NEOgHacking/DMXion_4Port_Node/Firmware/esp-at-5.0.0.0/docs/_static/about-esp-at-solution.png

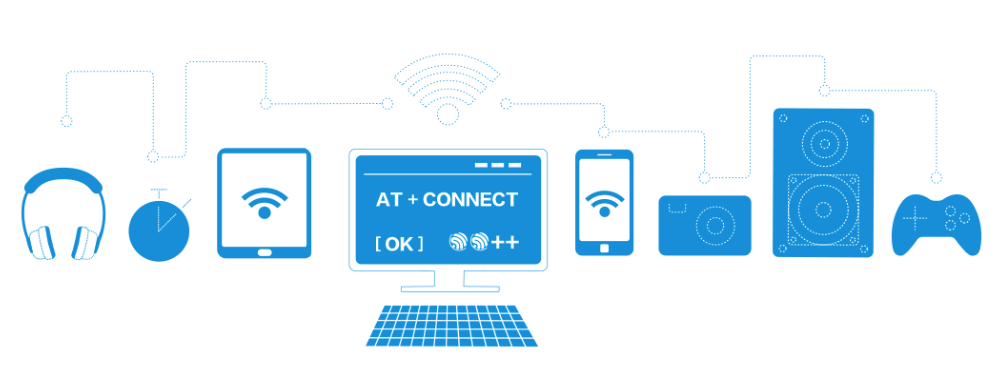
Firmware/esp-at-5.0.0.0/docs/_static/about-esp-at-solution.png
