NEOgHacking/DMXion_4Port_Node/Firmware/esp-at-5.0.0.0/docs/_static/at-sub-release-apply.png

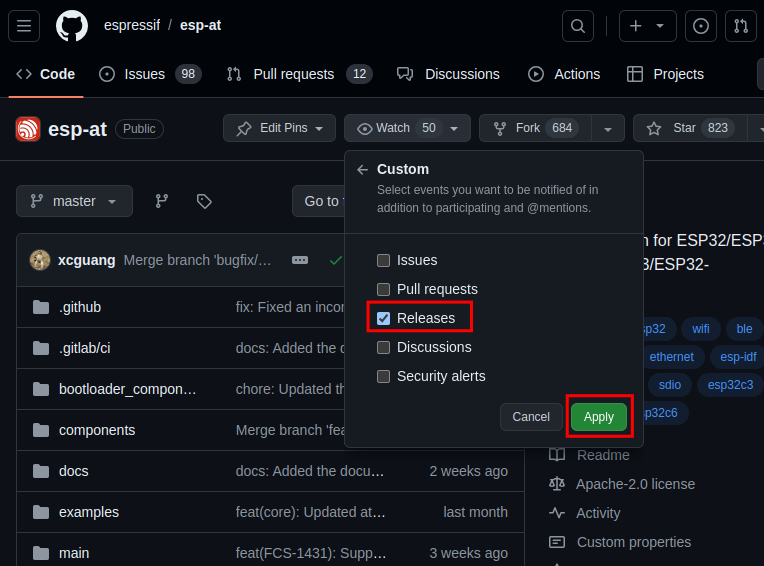
Firmware/esp-at-5.0.0.0/docs/_static/at-sub-release-apply.png
