NEOgHacking/DMXion_4Port_Node/Firmware/esp-at-5.0.0.0/docs/_static/at_command_examples/esp-power-consumption-hardware-connection.png

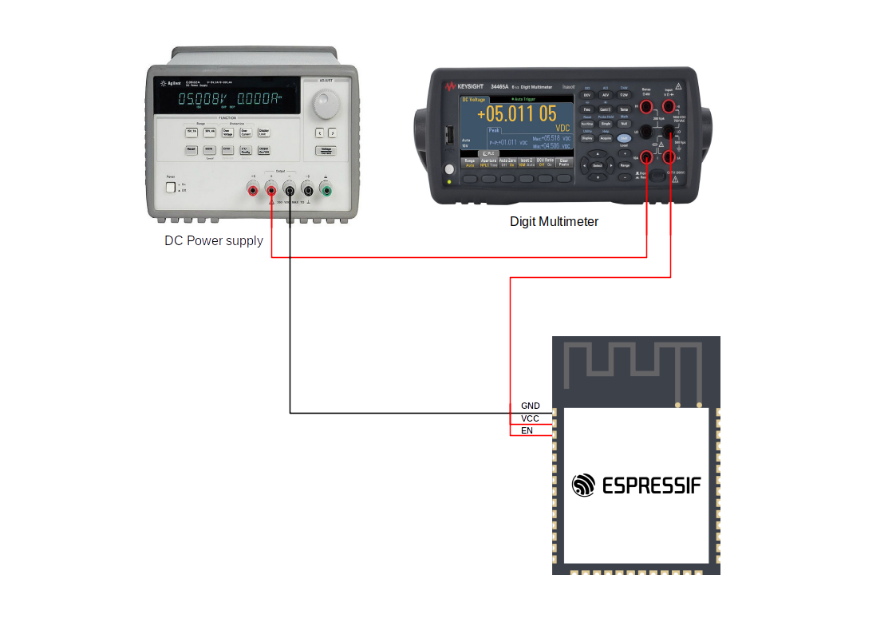
Firmware/esp-at-5.0.0.0/docs/_static/at_command_examples/esp-power-consumption-hardware-connection.png
