NEOgHacking/DMXion_4Port_Node/Firmware/esp-at-5.0.0.0/docs/_static/compile_and_develop/at-py-download.png

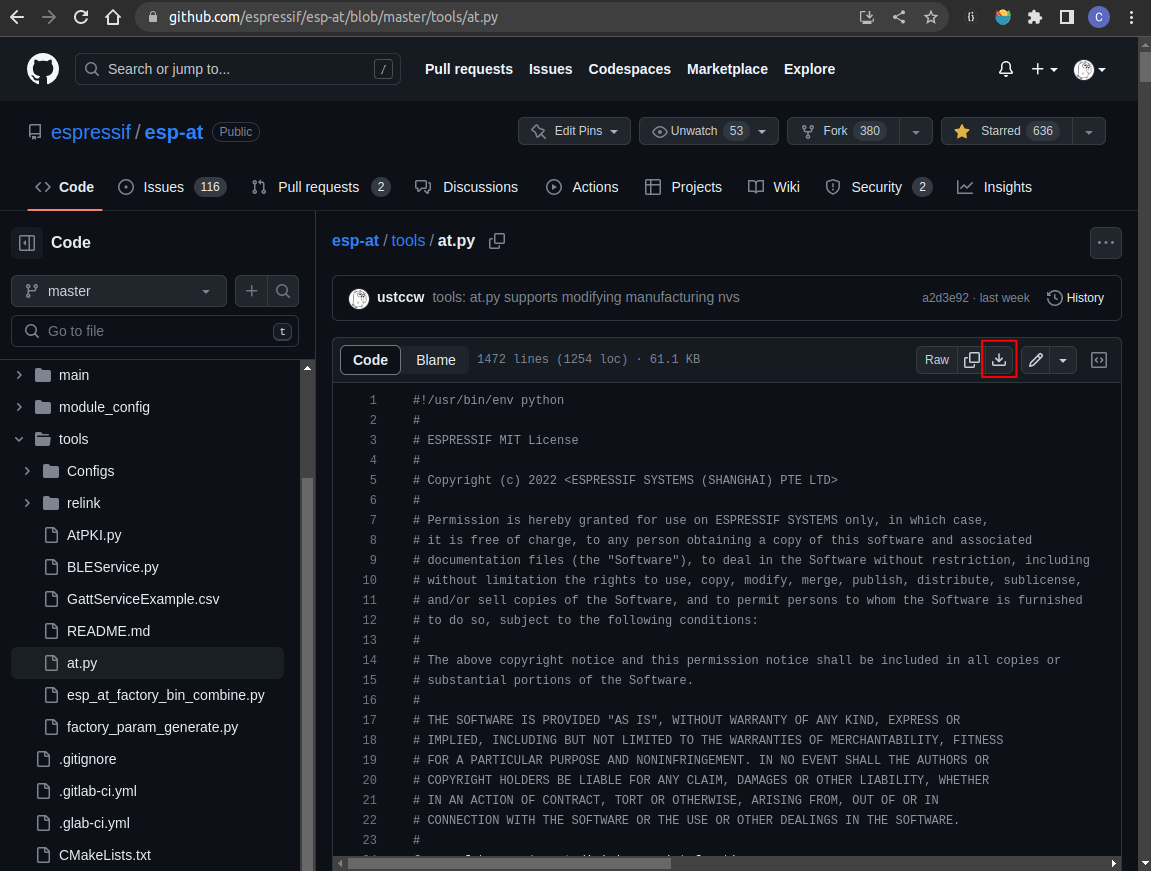
Firmware/esp-at-5.0.0.0/docs/_static/compile_and_develop/at-py-download.png
