NEOgHacking/DMXion_4Port_Node/Firmware/esp-at-5.0.0.0/docs/_static/compile_and_develop/ble_customize_service.png

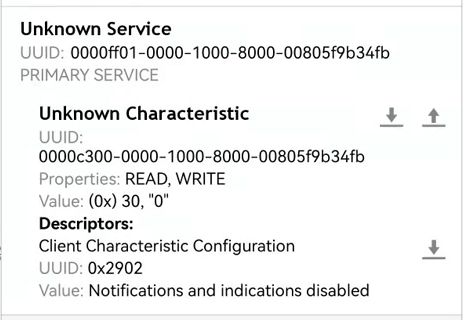
Firmware/esp-at-5.0.0.0/docs/_static/compile_and_develop/ble_customize_service.png
