NEOgHacking/DMXion_4Port_Node/Firmware/esp-at-5.0.0.0/docs/_static/download_temp_version/download-temp-version-github.png

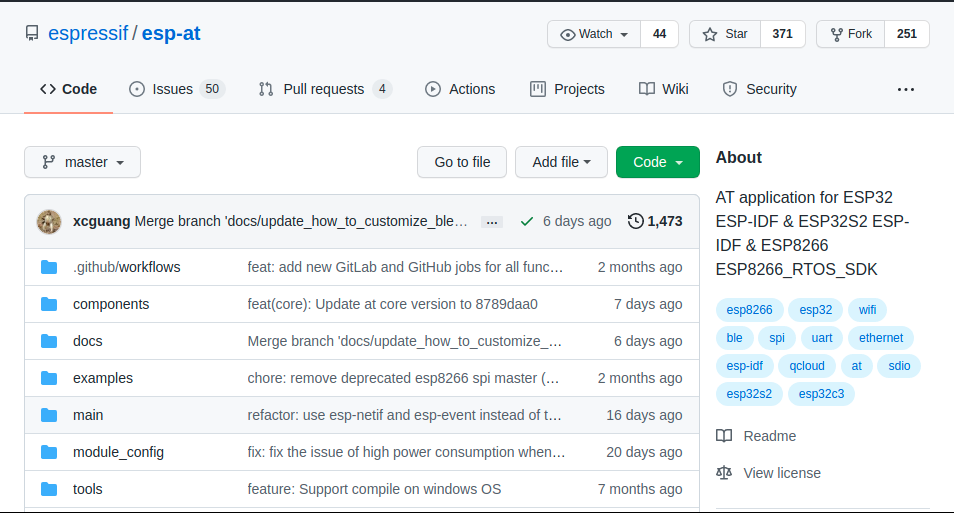
Firmware/esp-at-5.0.0.0/docs/_static/download_temp_version/download-temp-version-github.png
