NEOgHacking/DMXion_4Port_Node/Firmware/esp-at-5.0.0.0/docs/_static/ESP-AT-overview.jpg

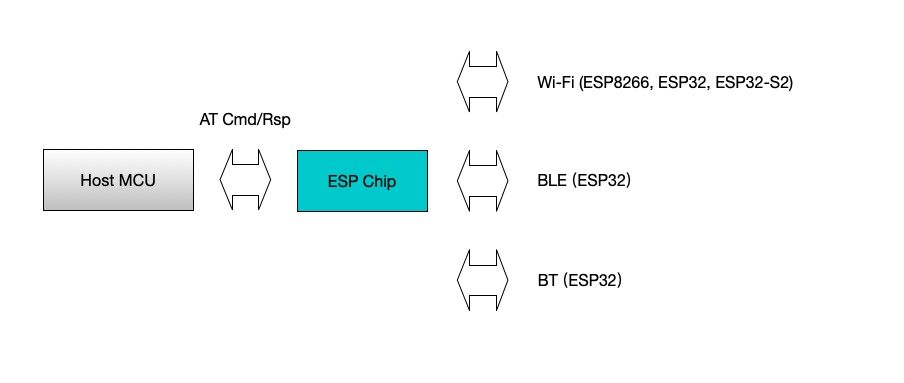
Firmware/esp-at-5.0.0.0/docs/_static/ESP-AT-overview.jpg
