NEOgHacking/DMXion_4Port_Node/Firmware/esp-at-5.0.0.0/docs/_static/get_started/hw_connection/esp32-pico-d4.png

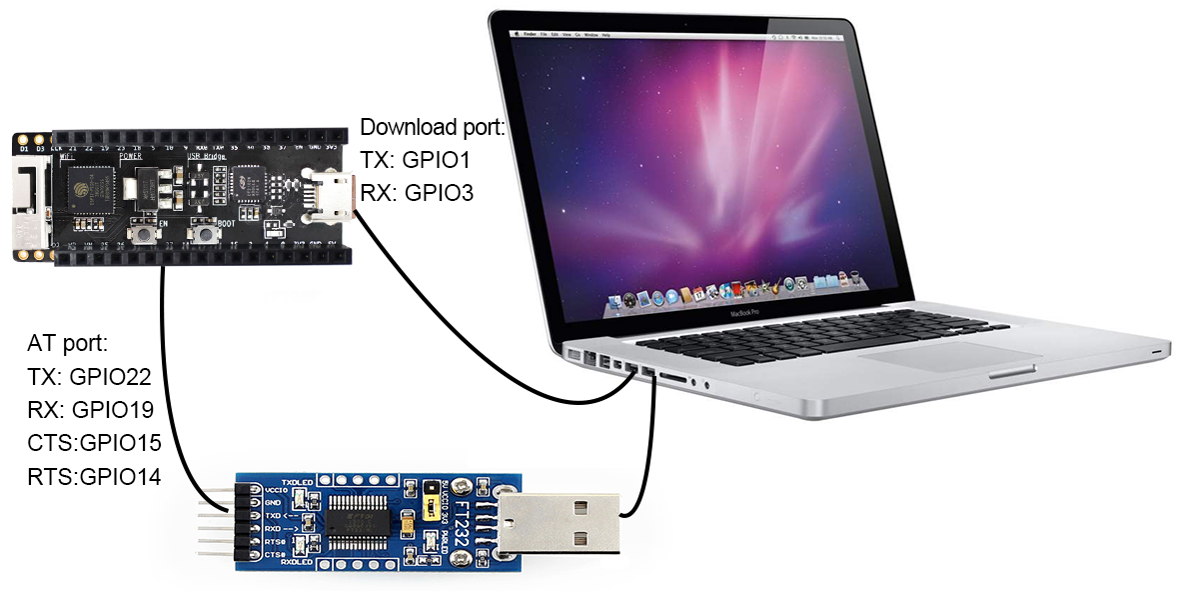
Firmware/esp-at-5.0.0.0/docs/_static/get_started/hw_connection/esp32-pico-d4.png
