NEOgHacking/DMXion_4Port_Node/Firmware/esp-at-5.0.0.0/docs/_static/get_started/hw_connection/hw-connection-what-you-need.png

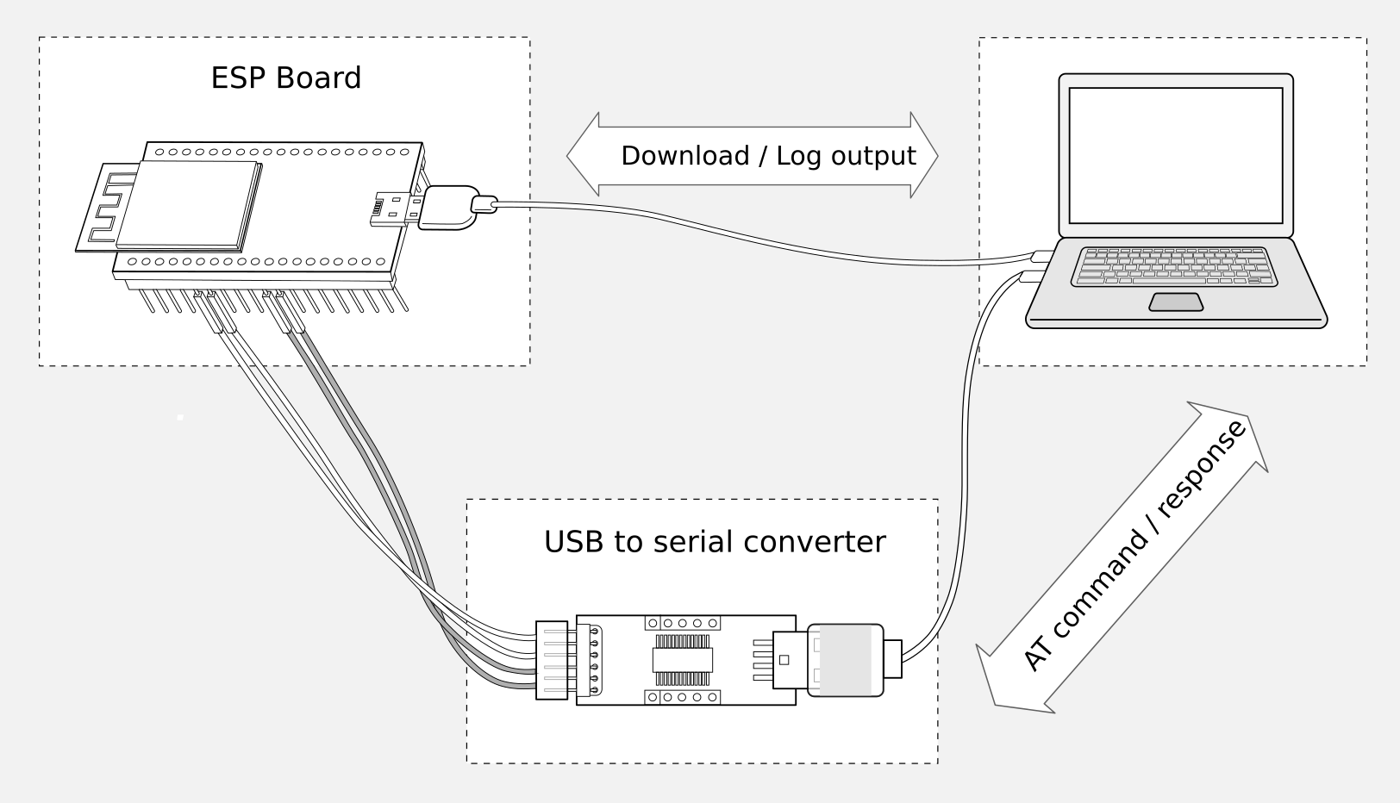
Firmware/esp-at-5.0.0.0/docs/_static/get_started/hw_connection/hw-connection-what-you-need.png
