NEOgHacking/DMXion_4Port_Node/Firmware/esp-at-5.0.0.0/docs/_static/hp-customized-at-commands-and-firmware.png

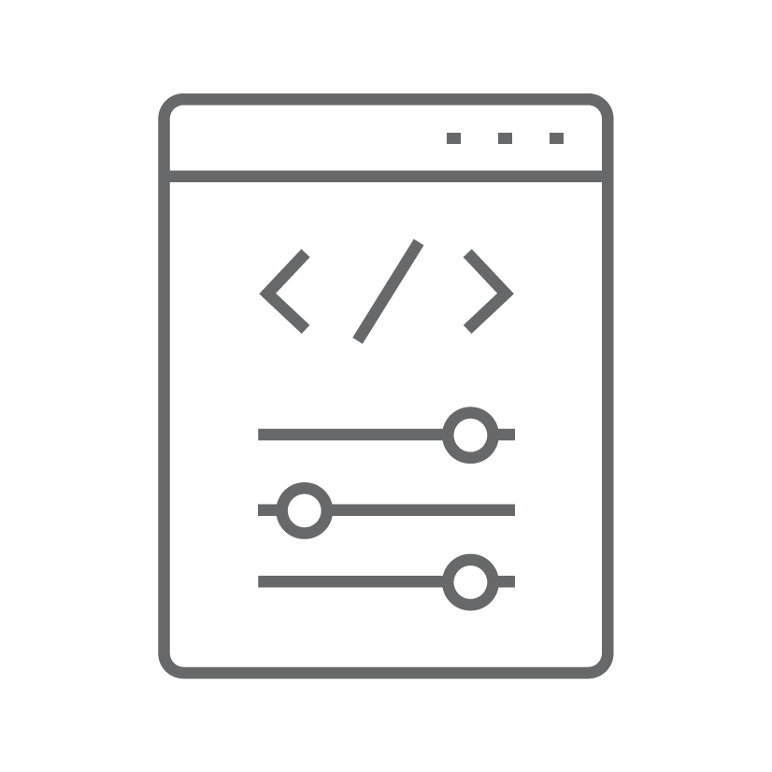
Firmware/esp-at-5.0.0.0/docs/_static/hp-customized-at-commands-and-firmware.png
