NEOgHacking/DMXion_4Port_Node/Firmware/esp-at-5.0.0.0/docs/_static/hp-get-started.png

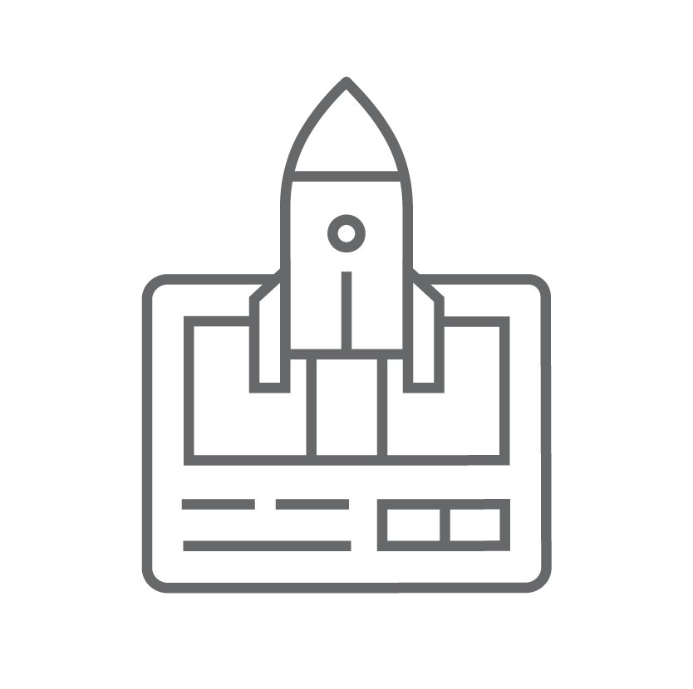
Firmware/esp-at-5.0.0.0/docs/_static/hp-get-started.png
