NEOgHacking/DMXion_4Port_Node/Firmware/esp-at-5.0.0.0/docs/_static/hp-index-of-abbreviations-and-acronyms.png

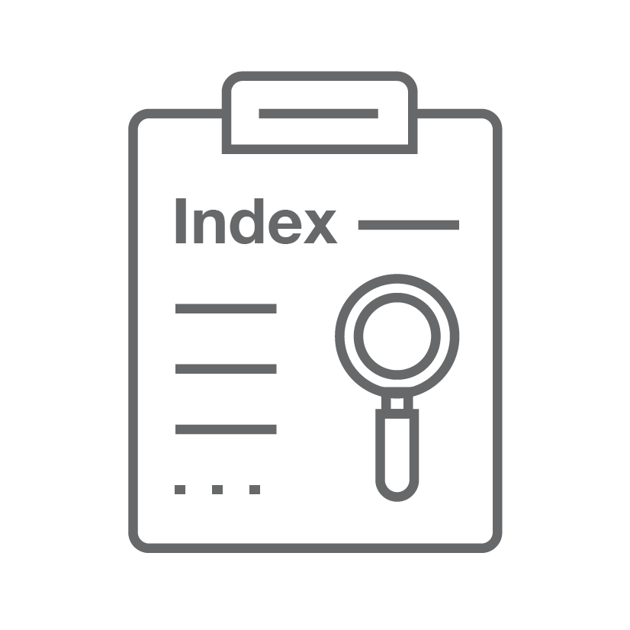
Firmware/esp-at-5.0.0.0/docs/_static/hp-index-of-abbreviations-and-acronyms.png
