NEOgHacking/DMXion_4Port_Node/Firmware/esp-at-5.0.0.0/docs/_static/web_compile/commit-change-s2.png

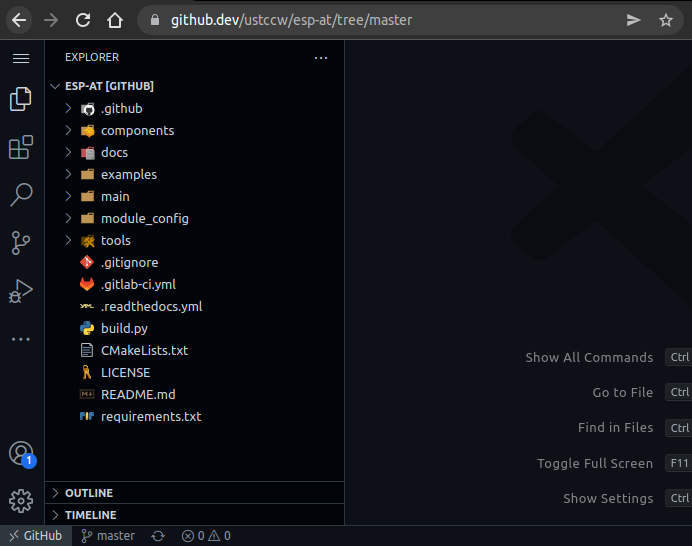
Firmware/esp-at-5.0.0.0/docs/_static/web_compile/commit-change-s2.png
