NEOgHacking/DMXion_4Port_Node/Firmware/esp-at-5.0.0.0/docs/_static/Web_server/captive_portal_auth_pages.png

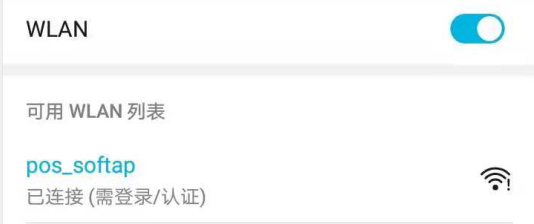
Firmware/esp-at-5.0.0.0/docs/_static/Web_server/captive_portal_auth_pages.png
