NEOgHacking/DMXion_4Port_Node/Firmware/esp-at-5.0.0.0/docs/_static/Web_server/web_brower_get_ap_record_en.png

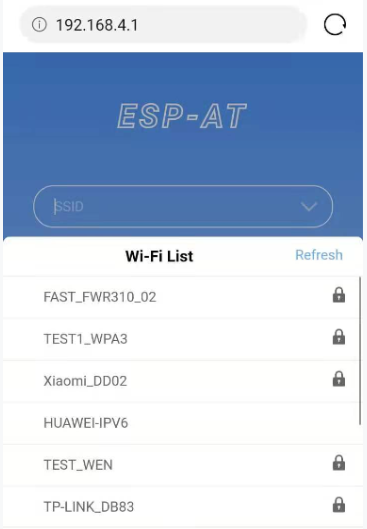
Firmware/esp-at-5.0.0.0/docs/_static/Web_server/web_brower_get_ap_record_en.png
