NEOgHacking/DMXion_4Port_Node/Firmware/esp-at-5.0.0.0/docs/_static/Web_server/web_brower_ota_chose_firmware.png

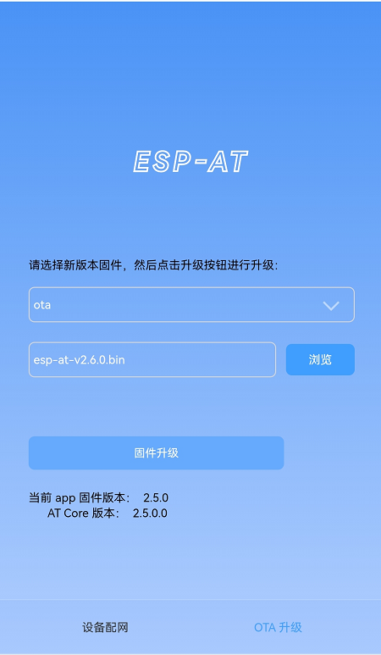
Firmware/esp-at-5.0.0.0/docs/_static/Web_server/web_brower_ota_chose_firmware.png
