NEOgHacking/DMXion_4Port_Node/Firmware/esp-at-5.0.0.0/docs/_static/Web_server/web_brower_wifi_ap_en.png

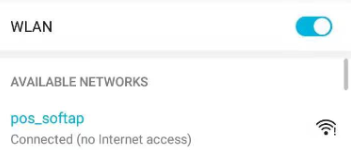
Firmware/esp-at-5.0.0.0/docs/_static/Web_server/web_brower_wifi_ap_en.png
