NEOgHacking/DMXion_4Port_Node/Firmware/esp-at-5.0.0.0/docs/_static/Web_server/web_wechat_connect_router.png

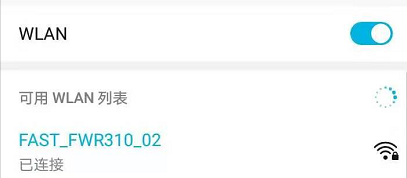
Firmware/esp-at-5.0.0.0/docs/_static/Web_server/web_wechat_connect_router.png
