NEOgHacking/DMXion_4Port_Node/Firmware/esp-at-5.0.0.0/docs/_static/Web_server/web_wechat_enter_local_password.png

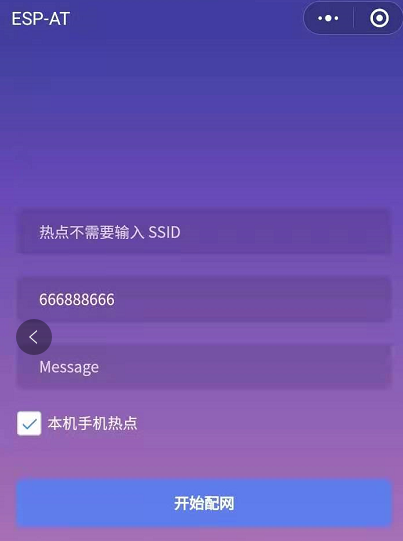
Firmware/esp-at-5.0.0.0/docs/_static/Web_server/web_wechat_enter_local_password.png
