NEOgHacking/DMXion_4Port_Node/Firmware/esp-at-5.0.0.0/docs/_static/Web_server/web_wechat_update_router_info.png

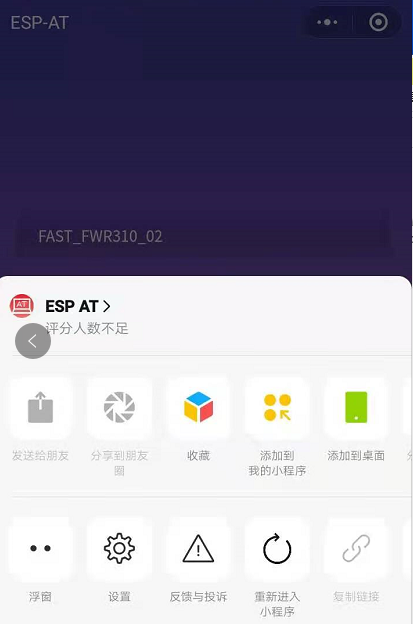
Firmware/esp-at-5.0.0.0/docs/_static/Web_server/web_wechat_update_router_info.png
