NEOgHacking/DMXion_4Port_Node/Firmware/esp-at-5.0.0.0/docs/img/esp32at-log.png

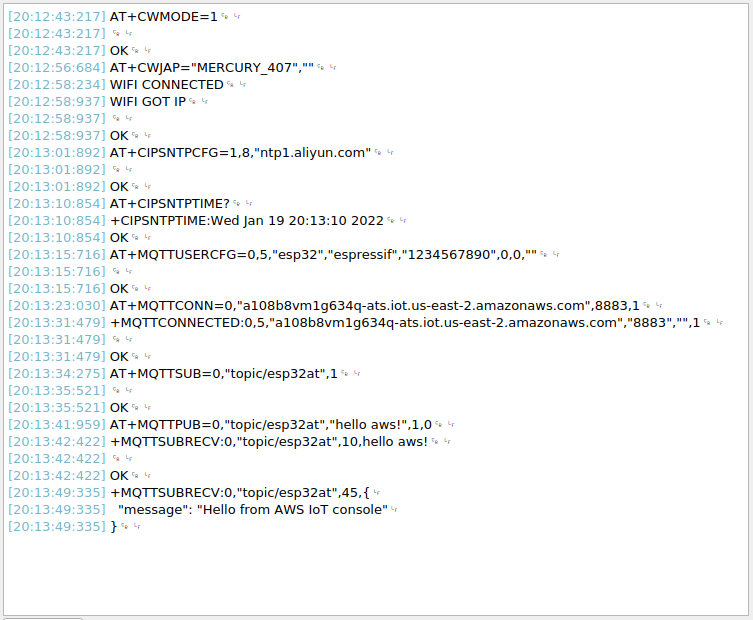
Firmware/esp-at-5.0.0.0/docs/img/esp32at-log.png
