NEOgHacking/DMXion_4Port_Node/Firmware/esp-at-5.0.0.0/examples/at_sdio_host/res/sdio_dataflow.jpg

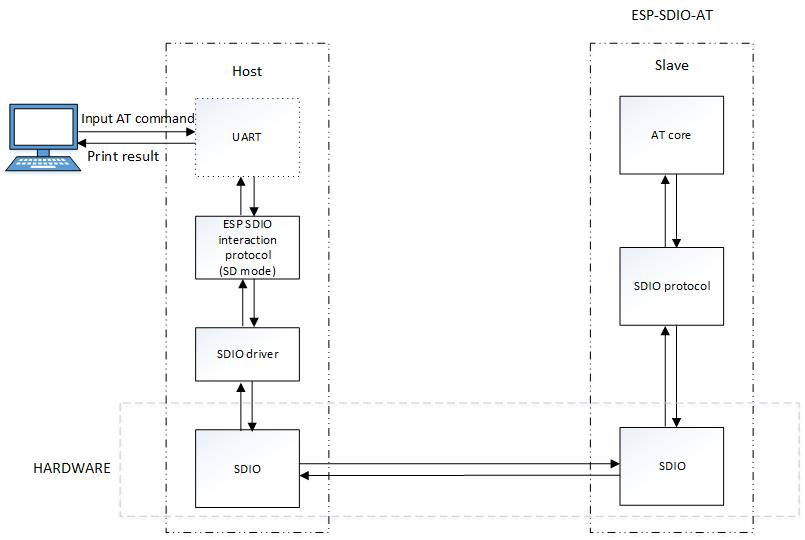
Firmware/esp-at-5.0.0.0/examples/at_sdio_host/res/sdio_dataflow.jpg
