NEOgHacking/DMXion_4Port_Node/Firmware/esp-at-5.0.0.0/examples/at_spi_master/sdspi/res/data_flow.png

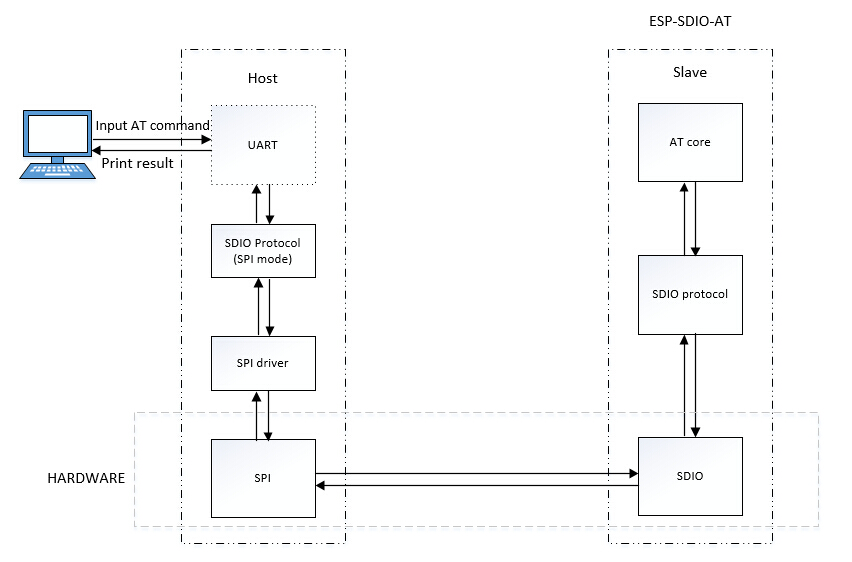
Firmware/esp-at-5.0.0.0/examples/at_spi_master/sdspi/res/data_flow.png
