NEOgHacking/DMXion_4Port_Node/Firmware/esp-at-5.0.0.0/examples/at_spi_master/spi/esp32_c_series/res/mcu_read_data.png

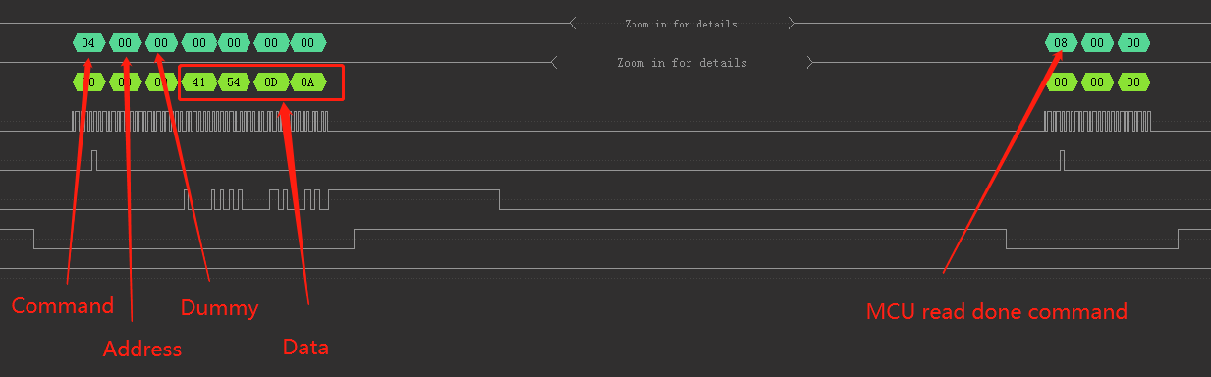
Firmware/esp-at-5.0.0.0/examples/at_spi_master/spi/esp32_c_series/res/mcu_read_data.png
