NEOgHacking/DMXion_4Port_Node/Firmware/esp-at-5.0.0.0/docs/zh_CN/Get_Started/Downloading_guide.rst

下载指导
==========

{IDF_TARGET_MODULE_NAME: default="undefined", esp32="ESP32-WROOM-32", esp32c2="ESP8684-MINI-1", esp32c3="ESP32-C3-MINI-1", esp32c5="ESP32-C5-WROOM-1", esp32c6="ESP32-C6-MINI-1", esp32c61="ESP32-C61-WROOM-1", esp32s2="ESP32-S2-MINI"}
{IDF_TARGET_FACTORY_BIN: default="undefined", esp32="ESP32-WROOM-32-AT-V3.2.0.0", esp32c2="ESP32C2-4MB-AT-V3.3.0.0", esp32c3="ESP32-C3-MINI-1-AT-V3.3.0.0", esp32c5="ESP32C5-4MB-AT-V5.0.0.0", esp32c6="ESP32C6-4MB-AT-V4.0.0.0", esp32c61="ESP32C61-4MB-AT-V5.0.0.0", esp32s2="ESP32-S2-MINI-AT-V3.4.0.0"}

:link_to_translation:`en:[English]`

本文档以 {IDF_TARGET_MODULE_NAME} 模组为例，介绍如何下载 {IDF_TARGET_MODULE_NAME} 模组对应的 AT 固件，以及如何将固件烧录到模组上，其它 {IDF_TARGET_NAME} 系列模组也可参考本文档。

下载和烧录 AT 固件之前，请确保您已正确连接所需硬件，具体可参考 :doc:`Hardware_connection`。

对于不同系列的模组，AT 默认固件所支持的命令会有所差异。具体可参考 :doc:`/Compile_and_Develop/esp-at_firmware_differences`。

.. _download-at-firmware:

下载 AT 固件
-------------

请按照以下步骤将 AT 固件下载至 PC：

- 前往 :doc:`../AT_Binary_Lists/index`
- 找到您的模组所对应的 AT 固件
- 点击相应链接进行下载

此处，我们下载了 {IDF_TARGET_MODULE_NAME} 对应的 ``{IDF_TARGET_FACTORY_BIN}`` 固件，该固件的目录结构及其中各个 bin 文件介绍如下，其它 {IDF_TARGET_NAME} 系列模组固件的目录结构及 bin 文件也可参考如下介绍：

.. code-block:: none

   .
   ├── at_customize.bin                 // 二级分区表
   ├── bootloader                       // bootloader
   │   └── bootloader.bin
   ├── customized_partitions            // AT 自定义 bin 文件
         ├── mfg_nvs.csv                  // 量产 NVS 分区的原始数据
   │   └── mfg_nvs.bin                  // 量产 NVS 分区 bin 文件
   ├── download.config                  // 烧录固件的参数
   ├── esp-at.bin                       // AT 应用固件
   ├── esp-at.elf
   ├── esp-at.map
   ├── factory                          // 量产所需打包好的 bin 文件
   │   └── factory_XXX.bin
   ├── flasher_args.json                // 下载参数信息新的格式
   ├── ota_data_initial.bin             // ota data 区初始值
   ├── partition_table                  // 一级分区列表
   │   └── partition-table.bin
   └── sdkconfig                        // AT 固件对应的编译配置

其中，``download.config`` 文件包含烧录固件的参数：

.. only:: esp32

   .. code-block:: none

      --flash_mode dio --flash_freq 40m --flash_size 4MB
      0x1000 bootloader/bootloader.bin
      0x8000 partition_table/partition-table.bin
      0x10000 ota_data_initial.bin
      0x20000 at_customize.bin
      0x21000 customized_partitions/mfg_nvs.bin
      0x100000 esp-at.bin

.. only:: esp32c2

   .. code-block:: none

      --flash_mode dio --flash_freq 60m --flash_size 4MB
      0x0 bootloader/bootloader.bin
      0x8000 partition_table/partition-table.bin
      0xd000 ota_data_initial.bin
      0x1e000 at_customize.bin
      0x1f000 customized_partitions/mfg_nvs.bin
      0x60000 esp-at.bin

.. only:: esp32c3

   .. code-block:: none

      --flash_mode dio --flash_freq 40m --flash_size 4MB
      0x0 bootloader/bootloader.bin
      0x8000 partition_table/partition-table.bin
      0xd000 ota_data_initial.bin
      0x1e000 at_customize.bin
      0x1f000 customized_partitions/mfg_nvs.bin
      0x60000 esp-at.bin

.. only:: esp32c5

   .. code-block:: none

      --flash_mode dio --flash_freq 80m --flash_size 4MB
      0x2000 bootloader/bootloader.bin
      0xc000 partition_table/partition-table.bin
      0xd000 ota_data_initial.bin
      0x30000 at_customize.bin
      0x31000 customized_partitions/mfg_nvs.bin
      0xa0000 esp-at.bin

.. only:: esp32c6

   .. code-block:: none

      --flash_mode dio --flash_freq 80m --flash_size 4MB
      0x0 bootloader/bootloader.bin
      0x8000 partition_table/partition-table.bin
      0xd000 ota_data_initial.bin
      0x1e000 at_customize.bin
      0x1f000 customized_partitions/mfg_nvs.bin
      0x60000 esp-at.bin

.. only:: esp32c61

   .. code-block:: none

      --flash_mode dio --flash_freq 80m --flash_size 4MB
      0x0 bootloader/bootloader.bin
      0xc000 partition_table/partition-table.bin
      0xd000 ota_data_initial.bin
      0x30000 at_customize.bin
      0x31000 customized_partitions/mfg_nvs.bin
      0xa0000 esp-at.bin

.. only:: esp32s2

   .. code-block:: none

      --flash_mode dio --flash_freq 80m --flash_size 4MB
      0x1000 bootloader/bootloader.bin
      0x8000 partition_table/partition-table.bin
      0x10000 ota_data_initial.bin
      0x20000 at_customize.bin
      0x21000 customized_partitions/mfg_nvs.bin
      0x100000 esp-at.bin

.. list::

   - ``--flash_mode dio`` 代表此固件采用的 flash dio 模式进行编译；
   :esp32 or esp32c3: - ``--flash_freq 40m`` 代表此固件采用的 flash 通讯频率为 40 MHz；
   :esp32c2: - ``--flash_freq 60m`` 代表此固件采用的 flash 通讯频率为 60 MHz；
   :esp32c5 or esp32c6 or esp32c61 or esp32s2: - ``--flash_freq 80m`` 代表此固件采用的 flash 通讯频率为 80 MHz；
   - ``--flash_size 4MB`` 代表此固件适用的 flash 最小为 4 MB；
   :esp32 or esp32s2: - ``0x10000 ota_data_initial.bin`` 代表在 ``0x10000`` 地址烧录 ``ota_data_initial.bin`` 文件。
   :esp32c2 or esp32c3 or esp32c5 or esp32c6 or esp32c61: - ``0xd000 ota_data_initial.bin`` 代表在 ``0xd000`` 地址烧录 ``ota_data_initial.bin`` 文件。

.. _flash-at-firmware-into-your-device:

烧录 AT 固件至设备
-------------------

请根据您的操作系统选择对应的烧录方法。

Windows
^^^^^^^^

开始烧录之前，请下载 Windows `Flash 下载工具 <https://dl.espressif.com/public/flash_download_tool.zip>`_，详细指导可参阅 `Flash 下载工具用户指南 <https://docs.espressif.com/projects/esp-test-tools/zh_CN/latest/{IDF_TARGET_PATH_NAME}/production_stage/tools/flash_download_tool.html>`_。

- 打开 Flash 下载工具；
- 选择芯片类型；（此处，我们选择 ``{IDF_TARGET_NAME}``。）
- 根据您的需求选择一种工作模式；（此处，我们选择 ``develop``。)
- 根据您的需求选择一种下载接口；（此处，我们选择 ``uart``。)

固件下载配置选择

   固件下载配置选择

- 将 AT 固件烧录至设备，以下两种方式任选其一：

   - 直接下载打包好的量产固件（即 ``build/factory`` 目录下的 ``factory_XXX.bin``）至 ``0x0`` 地址：勾选 "DoNotChgBin"，使用量产固件的默认配置；

     下载至单个地址界面图

        下载至单个地址界面图（点击放大）

   - 分开下载多个 bin 文件至不同的地址：根据 ``download.config`` 文件进行配置，请勿勾选 "DoNotChgBin"；

     下载至多个地址界面图

        下载至多个地址界面图（点击放大）

为了避免烧录出现问题，请查看开发板的下载接口的 COM 端口号，并从 "COM:" 下拉列表中选择该端口号。有关如何查看端口号的详细介绍请参考 `在 Windows 上查看端口 <https://docs.espressif.com/projects/esp-idf/zh_CN/latest/{IDF_TARGET_PATH_NAME}/get-started/establish-serial-connection.html#windows>`_。 

烧录完成后, 请 `检查 AT 固件是否烧录成功`_。

Linux 或 macOS
^^^^^^^^^^^^^^^

开始烧录之前，请安装 `esptool.py <https://github.com/espressif/esptool>`_。

以下两种方式任选其一，将 AT 固件烧录至设备：

- 分开下载多个 bin 文件至不同的地址：输入以下命令，替换 ``PORTNAME`` 和 ``download.config`` 参数；

  .. code-block:: none

      esptool.py --chip auto --port PORTNAME --baud 115200 --before default_reset --after hard_reset write_flash -z download.config

  将 ``PORTNAME`` 替换成开发板的下载接口名称，若您无法确定该接口名称，请参考 `在 Linux 和 macOS 上查看端口 <https://docs.espressif.com/projects/esp-idf/zh_CN/latest/{IDF_TARGET_PATH_NAME}/get-started/establish-serial-connection.html#linux-macos>`_。

  将 ``download.config`` 替换成该文件里的参数列表。

  以下是将固件烧录至 {IDF_TARGET_MODULE_NAME} 模组输入的命令：

   .. only:: esp32

      .. code-block:: none

         esptool.py --chip auto --port /dev/tty.usbserial-0001 --baud 115200 --before default_reset --after hard_reset write_flash -z --flash_mode dio --flash_freq 40m --flash_size 4MB 0x8000 partition_table/partition-table.bin 0x10000 ota_data_initial.bin 0x1000 bootloader/bootloader.bin 0x100000 esp-at.bin 0x20000 at_customize.bin 0x21000 customized_partitions/mfg_nvs.bin

   .. only:: esp32c2

      .. code-block:: none

         esptool.py --chip auto --port /dev/tty.usbserial-0001 --baud 115200 --before default_reset --after hard_reset write_flash -z --flash_mode dio --flash_freq 60m --flash_size 4MB 0x0 bootloader/bootloader.bin 0x60000 esp-at.bin 0x8000 partition_table/partition-table.bin 0xd000 ota_data_initial.bin 0x1e000 at_customize.bin 0x1f000 customized_partitions/mfg_nvs.bin

   .. only:: esp32c3

      .. code-block:: none

         esptool.py --chip auto --port /dev/tty.usbserial-0001 --baud 115200 --before default_reset --after hard_reset write_flash -z --flash_mode dio --flash_freq 40m --flash_size 4MB 0x8000 partition_table/partition-table.bin 0xd000 ota_data_initial.bin 0x0 bootloader/bootloader.bin 0x60000 esp-at.bin 0x1e000 at_customize.bin 0x1f000 customized_partitions/mfg_nvs.bin

   .. only:: esp32c5

      .. code-block:: none

         esptool.py --chip auto --port /dev/tty.usbserial-0001 --baud 115200 --before default_reset --after hard_reset write_flash -z --flash_mode dio --flash_freq 80m --flash_size 4MB 0xc000 partition_table/partition-table.bin 0xd000 ota_data_initial.bin 0x2000 bootloader/bootloader.bin 0xa0000 esp-at.bin 0x30000 at_customize.bin 0x31000 customized_partitions/mfg_nvs.bin

   .. only:: esp32c6

      .. code-block:: none

         esptool.py --chip auto --port /dev/tty.usbserial-0001 --baud 115200 --before default_reset --after hard_reset write_flash -z --flash_mode dio --flash_freq 80m --flash_size 4MB 0x8000 partition_table/partition-table.bin 0xd000 ota_data_initial.bin 0x0 bootloader/bootloader.bin 0x60000 esp-at.bin 0x1e000 at_customize.bin 0x1f000 customized_partitions/mfg_nvs.bin

   .. only:: esp32c61

      .. code-block:: none

         esptool.py --chip auto --port /dev/tty.usbserial-0001 --baud 115200 --before default_reset --after hard_reset write_flash -z --flash_mode dio --flash_freq 80m --flash_size 4MB 0xc000 partition_table/partition-table.bin 0xd000 ota_data_initial.bin 0x0 bootloader/bootloader.bin 0xa0000 esp-at.bin 0x30000 at_customize.bin 0x31000 customized_partitions/mfg_nvs.bin

   .. only:: esp32s2

      .. code-block:: none

         esptool.py --chip auto --port /dev/tty.usbserial-0001 --baud 115200 --before default_reset --after hard_reset write_flash -z --flash_mode dio --flash_freq 40m --flash_size 4MB 0x0 bootloader/bootloader.bin 0x60000 esp-at.bin 0x8000 partition_table/partition-table.bin 0xd000 ota_data_initial.bin 0x1e000 at_customize.bin 0x1f000 customized_partitions/mfg_nvs.bin

- 直接下载打包好的量产固件至 ``0x0`` 地址：输入以下命令，替换 ``PORTNAME`` 和 ``FILEDIRECTORY`` 参数；

  .. code-block:: none

     esptool.py --chip auto --port PORTNAME --baud 115200 --before default_reset --after hard_reset write_flash -z --flash_mode dio --flash_freq 40m --flash_size 4MB 0x0 FILEDIRECTORY

  将 ``PORTNAME`` 替换成开发板的下载接口名称，若您无法确定该接口名称，请参考 `在 Linux 和 macOS 上查看端口 <https://docs.espressif.com/projects/esp-idf/zh_CN/latest/{IDF_TARGET_PATH_NAME}/get-started/establish-serial-connection.html#linux-macos>`_。

  将 ``FILEDIRECTORY`` 替换成打包好的量产固件的文件路径，通常情况下，文件路径是 ``factory/XXX.bin``。

  以下是将固件烧录至 {IDF_TARGET_MODULE_NAME} 模组输入的命令：

   .. only:: esp32

      .. code-block:: none

         esptool.py --chip auto --port /dev/tty.usbserial-0001 --baud 115200 --before default_reset --after hard_reset write_flash -z --flash_mode dio --flash_freq 40m --flash_size 4MB 0x0 factory/factory_WROOM-32.bin

   .. only:: esp32c2

      .. code-block:: none

         esptool.py --chip auto --port /dev/tty.usbserial-0001 --baud 115200 --before default_reset --after hard_reset write_flash -z --flash_mode dio --flash_freq 60m --flash_size 4MB 0x0 factory/factory_ESP32C2-4MB.bin

   .. only:: esp32c3

      .. code-block:: none

         esptool.py --chip auto --port /dev/tty.usbserial-0001 --baud 115200 --before default_reset --after hard_reset write_flash -z --flash_mode dio --flash_freq 40m --flash_size 4MB 0x0 factory/factory_MINI-1.bin

   .. only:: esp32c5

      .. code-block:: none

         esptool.py --chip auto --port /dev/tty.usbserial-0001 --baud 115200 --before default_reset --after hard_reset write_flash -z --flash_mode dio --flash_freq 80m --flash_size 4MB 0x0 factory/factory_ESP32C5-4MB.bin

   .. only:: esp32c6

      .. code-block:: none

         esptool.py --chip auto --port /dev/tty.usbserial-0001 --baud 115200 --before default_reset --after hard_reset write_flash -z --flash_mode dio --flash_freq 80m --flash_size 4MB 0x0 factory/factory_ESP32C6-4MB.bin

   .. only:: esp32c61

      .. code-block:: none

         esptool.py --chip auto --port /dev/tty.usbserial-0001 --baud 115200 --before default_reset --after hard_reset write_flash -z --flash_mode dio --flash_freq 80m --flash_size 4MB 0x0 factory/factory_ESP32C61-4MB.bin

   .. only:: esp32s2

      .. code-block:: none

         esptool.py --chip auto --port /dev/tty.usbserial-0001 --baud 115200 --before default_reset --after hard_reset write_flash -z --flash_mode dio --flash_freq 80m --flash_size 4MB 0x0 factory/factory_MINI-1.bin

烧录完成后，请 `检查 AT 固件是否烧录成功`_。

.. _check-whether-at-works:

检查 AT 固件是否烧录成功
-------------------------

请按照以下步骤检查 AT 固件是否烧录成功：

- 打开串口工具，如 SecureCRT；
- 串口：选择用于发送或接收“AT 命令/响应”的串口（详情请见 :doc:`Hardware_connection`）；
- 波特率：115200；
- 数据位：8；
- 检验位：None；
- 停止位：1；
- 流控：None；
- 输入 "AT+GMR" 命令，并且换行 (CR LF)；

若如下所示，响应是 ``OK``, 则表示 AT 固件烧录成功。

.. only:: esp32c2

   .. code-block:: none

      AT+GMR
      AT version:3.3.0.0(3b13d04 - ESP32C2 - May  8 2024 08:21:45)
      SDK version:v5.0.6-dirty
      compile time(be332568):May  8 2024 08:50:59
      Bin version:v3.3.0.0(ESP32C2-4MB)

      OK

.. only:: esp32c3

   .. code-block:: none

      AT+GMR
      AT version:3.3.0.0(3b13d04 - ESP32C3 - May  8 2024 08:21:54)
      SDK version:v5.0.6-dirty
      compile time(be332568):May  8 2024 08:51:33
      Bin version:v3.3.0.0(MINI-1)

      OK

.. only:: esp32c5

   .. code-block:: none

      AT+GMR
      AT version:5.0.0.0(b0fe7e5 - ESP32C5 - Aug 22 2025 09:44:01)
      SDK version:v5.5-beta1-695-ga3ca8669f24
      compile time(7917c1fb):Aug 25 2025 15:10:23
      Bin version:v5.0.0.0(ESP32C5-4MB)

      OK

.. only:: esp32c6

   .. code-block:: none

      AT+GMR
      AT version:4.0.0.0(3fe3806 - ESP32C6 - Dec 29 2023 11:10:21)
      SDK version:v5.1.2-dirty
      compile time(89040be7):Jan  2 2024 05:53:07
      Bin version:v4.0.0.0(ESP32C6-4MB)

      OK

.. only:: esp32c61

   .. code-block:: none

      AT+GMR
      AT version:5.0.0.0(f6b0e89 - ESP32C61 - Oct 17 2025 08:55:06)
      SDK version:v5.5.1-255-g07e9bf4970
      compile time(65202f43):Oct 17 2025 19:46:13
      Bin version:v5.0.0.0(ESP32C61-4MB)

      OK

.. only:: esp32

   .. code-block:: none

      AT+GMR
      AT version:3.2.0.0(s-ec2dec2 - ESP32 - Jul 28 2023 07:05:28)
      SDK version:v5.0.2-376-g24b9d38a24-dirty
      compile time(6118fc22):Jul 28 2023 09:47:28
      Bin version:v3.2.0.0(WROOM-32)

      OK

.. only:: esp32s2

   .. code-block:: none

      AT+GMR
      AT version:3.4.0.0-dev(ca45add - ESP32S2 - May  9 2024 08:00:07)
      SDK version:v5.0.6-dirty
      compile time(877c7e69):May 10 2024 06:47:54
      Bin version:v3.4.0.0-dev(MINI)

      OK

否则，您需要通过以下方式之一检查 {IDF_TARGET_NAME} 设备开机日志：
  
**方法 1：**

- 打开串口工具，如 SecureCRT；
- 串口：选择用于“下载固件/输出日志”的串口，串口详情请参阅 :doc:`Hardware_connection`。
- 波特率：115200；
- 数据位：8；
- 检验位：None；
- 停止位：1；
- 流控：None；
- 直接按开发板的 RST 键，若日志和下面的日志相似，则说明 ESP-AT 固件已经正确初始化了。

**方法 2：**

- 打开两个串口工具，如 SecureCRT；
- 串口：分别选择用于发送或接收“AT 命令/响应”的串口以及用于“下载固件/输出日志”的串口，串口详情请参阅 :doc:`Hardware_connection`。
- 波特率：115200；
- 数据位：8；
- 检验位：None；
- 停止位：1；
- 流控：None；
- 在发送或接收“AT 命令/响应”的串口输入 :ref:`AT+RST <cmd-RST>` 命令，并且换行 (CR LF)，若“下载固件/输出日志”的串口日志和下面的日志相似，则说明 ESP-AT 固件已经正确初始化了。

.. only:: esp32

   {IDF_TARGET_NAME} 开机日志：

   .. code-block:: none

      rst:0x1 (POWERON_RESET),boot:0x13 (SPI_FAST_FLASH_BOOT)
      configsip: 0, SPIWP:0xee
      clk_drv:0x00,q_drv:0x00,d_drv:0x00,cs0_drv:0x00,hd_drv:0x00,wp_drv:0x00
      mode:DIO, clock div:2
      load:0x3fff0030,len:5884
      ho 0 tail 12 room 4
      load:0x40078000,len:15844
      load:0x40080400,len:3560
      entry 0x40080604
      I (29) boot: ESP-IDF v5.0-541-g885e501d99-dirty 2nd stage bootloader
      I (29) boot: compile time 08:40:13
      I (29) boot: chip revision: v1.0
      I (34) boot.esp32: SPI Speed      : 40MHz
      I (38) boot.esp32: SPI Mode       : DIO
      I (43) boot.esp32: SPI Flash Size : 4MB
      I (47) boot: Enabling RNG early entropy source...
      I (53) boot: Partition Table:
      I (56) boot: ## Label            Usage          Type ST Offset   Length
      I (64) boot:  0 phy_init         RF data          01 01 0000f000 00001000
      I (71) boot:  1 otadata          OTA data         01 00 00010000 00002000
      I (78) boot:  2 nvs              WiFi data        01 02 00012000 0000e000
      I (86) boot:  3 at_customize     unknown          40 00 00020000 000e0000
      I (93) boot:  4 ota_0            OTA app          00 10 00100000 00180000
      I (101) boot:  5 ota_1            OTA app          00 11 00280000 00180000
      I (108) boot: End of partition table
      I (113) esp_image: segment 0: paddr=00100020 vaddr=3f400020 size=1a854h (108628) map
      I (161) esp_image: segment 1: paddr=0011a87c vaddr=3ff80063 size=00008h (     8) load
      I (161) esp_image: segment 2: paddr=0011a88c vaddr=3ffbdb60 size=04d5ch ( 19804) load
      I (174) esp_image: segment 3: paddr=0011f5f0 vaddr=40080000 size=00a28h (  2600) load
      I (176) esp_image: segment 4: paddr=00120020 vaddr=400d0020 size=11f5c0h (1177024) map
      I (609) esp_image: segment 5: paddr=0023f5e8 vaddr=40080a28 size=1e948h (125256) load
      I (660) esp_image: segment 6: paddr=0025df38 vaddr=400c0000 size=00064h (   100) load
      I (676) boot: Loaded app from partition at offset 0x100000
      I (676) boot: Disabling RNG early entropy source...
      no external 32k oscillator, disable it now.
      at param mode: 1
      AT cmd port:uart1 tx:17 rx:16 cts:15 rts:14 baudrate:115200
      module_name: WROOM-32
      max tx power=78, ret=0
      2.5.0

.. only:: esp32c2

   {IDF_TARGET_NAME} 开机日志:

   .. code-block:: none

      ESP-ROM:esp8684-api2-20220127
      Build:Jan 27 2022
      rst:0x1 (POWERON),boot:0xc (SPI_FAST_FLASH_BOOT)
      SPIWP:0xee
      mode:DIO, clock div:1
      load:0x3fcd6108,len:0x18b0
      load:0x403ae000,len:0x854
      load:0x403b0000,len:0x2724
      entry 0x403ae000
      I (32) boot: ESP-IDF v5.0-dev-5949-g885e501d99-dirty 2nd stage bootloader
      I (32) boot: compile time 11:05:11
      I (32) boot: chip revision: v1.0
      I (36) boot.esp32c2: MMU Page Size  : 64K
      I (41) boot.esp32c2: SPI Speed      : 60MHz
      I (46) boot.esp32c2: SPI Mode       : DIO
      I (50) boot.esp32c2: SPI Flash Size : 4MB
      I (55) boot: Enabling RNG early entropy source...
      I (61) boot: Partition Table:
      I (64) boot: ## Label            Usage          Type ST Offset   Length
      I (71) boot:  0 otadata          OTA data         01 00 0000d000 00002000
      I (79) boot:  1 phy_init         RF data          01 01 0000f000 00001000
      I (86) boot:  2 nvs              WiFi data        01 02 00010000 0000e000
      I (94) boot:  3 at_customize     unknown          40 00 0001e000 00042000
      I (101) boot:  4 ota_0            OTA app          00 10 00060000 001d0000
      I (109) boot:  5 ota_1            OTA app          00 11 00230000 001d0000
      I (116) boot: End of partition table
      I (121) esp_image: segment 0: paddr=00060020 vaddr=3c0e0020 size=288c8h (166088) map
      I (167) esp_image: segment 1: paddr=000888f0 vaddr=3fca6010 size=02c18h ( 11288) load
      I (170) esp_image: segment 2: paddr=0008b510 vaddr=40380000 size=04b08h ( 19208) load
      I (178) esp_image: segment 3: paddr=00090020 vaddr=42000020 size=d444ch (869452) map
      I (378) esp_image: segment 4: paddr=00164474 vaddr=40384b08 size=01508h (  5384) load
      I (382) boot: Loaded app from partition at offset 0x60000
      I (383) boot: Disabling RNG early entropy source...
      at param mode: 1
      AT cmd port:uart1 tx:7 rx:6 cts:5 rts:4 baudrate:115200
      module_name: ESP32C2-4MB
      max tx power=78, ret=0
      3.0.0

.. only:: esp32c3

   {IDF_TARGET_NAME} 开机日志:

   .. code-block:: none

      ESP-ROM:esp32c3-api1-20210207
      Build:Feb  7 2021
      rst:0x1 (POWERON),boot:0xc (SPI_FAST_FLASH_BOOT)
      SPIWP:0xee
      mode:DIO, clock div:2
      load:0x3fcd5820,len:0x16b4
      load:0x403cc710,len:0x970
      load:0x403ce710,len:0x2e90
      entry 0x403cc710
      I (31) boot: ESP-IDF v5.0-541-g885e501d99-dirty 2nd stage bootloader
      I (31) boot: compile time 14:34:08
      I (32) boot: chip revision: v0.3
      I (35) boot.esp32c3: SPI Speed      : 40MHz
      I (40) boot.esp32c3: SPI Mode       : DIO
      I (45) boot.esp32c3: SPI Flash Size : 4MB
      I (49) boot: Enabling RNG early entropy source...
      I (55) boot: Partition Table:
      I (58) boot: ## Label            Usage          Type ST Offset   Length
      I (66) boot:  0 otadata          OTA data         01 00 0000d000 00002000
      I (73) boot:  1 phy_init         RF data          01 01 0000f000 00001000
      I (81) boot:  2 nvs              WiFi data        01 02 00010000 0000e000
      I (88) boot:  3 at_customize     unknown          40 00 0001e000 00042000
      I (95) boot:  4 ota_0            OTA app          00 10 00060000 001d0000
      I (103) boot:  5 ota_1            OTA app          00 11 00230000 001d0000
      I (110) boot: End of partition table
      I (115) esp_image: segment 0: paddr=00060020 vaddr=3c170020 size=3bd30h (245040) map
      I (175) esp_image: segment 1: paddr=0009bd58 vaddr=3fc95400 size=03884h ( 14468) load
      I (178) esp_image: segment 2: paddr=0009f5e4 vaddr=40380000 size=00a34h (  2612) load
      I (181) esp_image: segment 3: paddr=000a0020 vaddr=42000020 size=167a10h (1473040) map
      I (497) esp_image: segment 4: paddr=00207a38 vaddr=40380a34 size=1486ch ( 84076) load
      I (518) esp_image: segment 5: paddr=0021c2ac vaddr=50000000 size=00018h (    24) load
      I (525) boot: Loaded app from partition at offset 0x60000
      I (525) boot: Disabling RNG early entropy source...
      no external 32k oscillator, disable it now.
      at param mode: 1
      AT cmd port:uart1 tx:7 rx:6 cts:5 rts:4 baudrate:115200
      module_name: MINI-1
      max tx power=78, ret=0
      2.5.0

.. only:: esp32c5

   {IDF_TARGET_NAME} 开机日志:

   .. code-block:: none

      ESP-ROM:esp32c5-eco2-20250121
      Build:Jan 21 2025
      rst:0x1 (POWERON),boot:0x58 (SPI_FAST_FLASH_BOOT)
      SPI mode:DIO, clock div:1
      load:0x408556b0,len:0x1710
      load:0x4084bba0,len:0xd7c
      load:0x4084e5a0,len:0x31bc
      entry 0x4084bbaa
      I (23) boot: ESP-IDF v5.5-beta1-695-ga3ca8669f24-dir 2nd stage bootloader
      I (24) boot: compile time Aug 25 2025 15:10:14
      I (24) boot: chip revision: v1.0
      I (26) boot: efuse block revision: v0.2
      I (29) boot.esp32c5: SPI Speed      : 80MHz
      I (33) boot.esp32c5: SPI Mode       : DIO
      I (37) boot.esp32c5: SPI Flash Size : 4MB
      I (41) boot: Enabling RNG early entropy source...
      I (45) boot: Partition Table:
      I (48) boot: ## Label            Usage          Type ST Offset   Length
      I (54) boot:  0 otadata          OTA data         01 00 0000d000 00002000
      I (60) boot:  1 phy_init         RF data          01 01 0000f000 00001000
      I (67) boot:  2 nvs              WiFi data        01 02 00010000 0000e000
      I (73) boot:  3 at_customize     unknown          40 00 0001e000 00042000
      I (80) boot:  4 ota_0            OTA app          00 10 00060000 001d0000
      I (86) boot:  5 ota_1            OTA app          00 11 00230000 001d0000
      I (93) boot: End of partition table
      I (97) esp_image: segment 0: paddr=00060020 vaddr=42170020 size=2c954h (182612) map
      I (136) esp_image: segment 1: paddr=0008c97c vaddr=40800000 size=0369ch ( 13980) load
      I (139) esp_image: segment 2: paddr=00090020 vaddr=42000020 size=16d640h (1496640) map
      I (396) esp_image: segment 3: paddr=001fd668 vaddr=4080369c size=196d0h (104144) load
      I (417) esp_image: segment 4: paddr=00216d40 vaddr=4081cd80 size=04998h ( 18840) load
      I (421) esp_image: segment 5: paddr=0021b6e0 vaddr=50000000 size=000a4h (   164) load
      I (428) boot: Loaded app from partition at offset 0x60000
      I (429) boot: Disabling RNG early entropy source...
      I (927) at-init: at param mode: 1
      I (1554) at-uart: AT cmd port:uart1 tx:23 rx:24 cts:25 rts:26 baudrate:115200
      I (1555) at-init: module_name: ESP32C5-4MB
      I (1557) at-init: max tx power=78, ret=0
      I (1560) at-init: v5.0.0.0 (gitlab)
      I (2752) at-wifi: negotiated phy mode: 4

.. only:: esp32c6

   {IDF_TARGET_NAME} 开机日志:

   .. code-block:: none

      ESP-ROM:esp32c6-20220919
      Build:Sep 19 2022
      rst:0xc (SW_CPU),boot:0x6c (SPI_FAST_FLASH_BOOT)
      Saved PC:0x4001975a
      SPIWP:0xee
      mode:DIO, clock div:2
      load:0x4086c410,len:0xd50
      load:0x4086e610,len:0x2d74
      load:0x40875720,len:0x1800
      entry 0x4086c410
      I (27) boot: ESP-IDF v5.0-dev-9643-g4bc762621d-dirty 2nd stage bootloader
      I (27) boot: compile time Jul  5 2023 11:12:16
      I (29) boot: chip revision: v0.1
      I (32) boot.esp32c6: SPI Speed      : 40MHz
      I (37) boot.esp32c6: SPI Mode       : DIO
      I (41) boot.esp32c6: SPI Flash Size : 4MB
      I (46) boot: Enabling RNG early entropy source...
      I (52) boot: Partition Table:
      I (55) boot: ## Label            Usage          Type ST Offset   Length
      I (62) boot:  0 otadata          OTA data         01 00 0000d000 00002000
      I (70) boot:  1 phy_init         RF data          01 01 0000f000 00001000
      I (77) boot:  2 nvs              WiFi data        01 02 00010000 0000e000
      I (85) boot:  3 at_customize     unknown          40 00 0001e000 00042000
      I (92) boot:  4 ota_0            OTA app          00 10 00060000 001d0000
      I (100) boot:  5 ota_1            OTA app          00 11 00230000 001d0000
      I (107) boot: End of partition table
      I (112) esp_image: segment 0: paddr=00060020 vaddr=42140020 size=30628h (198184) map
      I (198) esp_image: segment 1: paddr=00090650 vaddr=40800000 size=0f9c8h ( 63944) load
      I (228) esp_image: segment 2: paddr=000a0020 vaddr=42000020 size=13c688h (1296008) map
      I (740) esp_image: segment 3: paddr=001dc6b0 vaddr=4080f9c8 size=05bf4h ( 23540) load
      I (752) esp_image: segment 4: paddr=001e22ac vaddr=408155c0 size=03c54h ( 15444) load
      I (760) esp_image: segment 5: paddr=001e5f08 vaddr=50000000 size=00068h (   104) load
      I (771) boot: Loaded app from partition at offset 0x60000
      I (772) boot: Disabling RNG early entropy source...
      no external 32k oscillator, disable it now.
      at param mode: 1
      AT cmd port:uart1 tx:7 rx:6 cts:5 rts:4 baudrate:115200
      module_name: ESP32C6-4MB
      max tx power=78, ret=0
      4.0.0

.. only:: esp32c61

   {IDF_TARGET_NAME} 开机日志:

   .. code-block:: none

      ESP-ROM:esp32c61-eco3-20250228
      Build:Feb 28 2025
      rst:0xc (SW_CPU),boot:0xc (SPI_FAST_FLASH_BOOT)
      Core0 Saved PC:0x4080a438
      SPI mode:DIO, clock div:1
      load:0x40845c00,len:0x1b80
      load:0x4083bd70,len:0xce4
      load:0x4083ea70,len:0x3248
      load:0x4084a000,len:0x222c
      entry 0x4083bd7a
      I (29) boot: ESP-IDF v5.5.1-255-g07e9bf4970-dirty 2nd stage bootloader
      I (30) boot: compile time Oct 17 2025 19:46:05
      I (32) boot: chip revision: v1.0
      I (32) boot: efuse block revision: v0.1
      I (35) boot.esp32c61: SPI Speed      : 80MHz
      I (39) boot.esp32c61: SPI Mode       : DIO
      I (43) boot.esp32c61: SPI Flash Size : 4MB
      I (47) boot: Enabling RNG early entropy source...
      I (51) boot: Partition Table:
      I (54) boot: ## Label            Usage          Type ST Offset   Length
      I (60) boot:  0 otadata          OTA data         01 00 0000d000 00002000
      I (67) boot:  1 phy_init         RF data          01 01 0000f000 00001000
      I (73) boot:  2 nvs              WiFi data        01 02 00010000 00020000
      I (80) boot:  3 at_customize     unknown          40 00 00030000 00070000
      I (86) boot:  4 ota_0            OTA app          00 10 000a0000 00220000
      I (93) boot:  5 ota_1            OTA app          00 11 002c0000 00140000
      I (100) boot: End of partition table
      I (103) esp_image: segment 0: paddr=000a0020 vaddr=42170020 size=2d18ch (184716) map
      I (157) esp_image: segment 1: paddr=000cd1b4 vaddr=40800000 size=02e64h ( 11876) load
      I (162) esp_image: segment 2: paddr=000d0020 vaddr=42000020 size=16ccb8h (1494200) map
      I (533) esp_image: segment 3: paddr=0023cce0 vaddr=40802e64 size=0ff78h ( 65400) load
      I (555) esp_image: segment 4: paddr=0024cc60 vaddr=40812e00 size=0416ch ( 16748) load
      I (570) boot: Loaded app from partition at offset 0xa0000
      I (571) boot: Disabling RNG early entropy source...
      I (1087) at-init: at param mode: 1
      I (1177) at-uart: AT cmd port:uart1 tx:6 rx:5 cts:4 rts:3 baudrate:115200
      I (1178) at-init: module_name: ESP32C61-4MB
      I (1179) at-init: max tx power=78, ret=0
      I (1181) at-init: v5.0.0.0 (gitlab)

.. only:: esp32s2

   {IDF_TARGET_NAME} startup log:

   .. code-block:: none

      ESP-ROM:esp32s2-rc4-20191025
      Build:Oct 25 2019
      rst:0x1 (POWERON),boot:0x8 (SPI_FAST_FLASH_BOOT)
      SPIWP:0xee
      mode:DIO, clock div:1
      load:0x3ffe6108,len:0x17d4
      load:0x4004c000,len:0xa9c
      load:0x40050000,len:0x3204
      entry 0x4004c1b8
      I (21) boot: ESP-IDF v5.0.6-dirty 2nd stage bootloader
      I (21) boot: compile time 06:47:54
      I (21) boot: chip revision: v0.0
      I (24) boot.esp32s2: SPI Speed      : 80MHz
      I (29) boot.esp32s2: SPI Mode       : DIO
      I (34) boot.esp32s2: SPI Flash Size : 4MB
      I (39) boot: Enabling RNG early entropy source...
      I (44) boot: Partition Table:
      I (48) boot: ## Label            Usage          Type ST Offset   Length
      I (55) boot:  0 phy_init         RF data          01 01 0000f000 00001000
      I (62) boot:  1 otadata          OTA data         01 00 00010000 00002000
      I (70) boot:  2 nvs              WiFi data        01 02 00012000 0000e000
      I (77) boot:  3 at_customize     unknown          40 00 00020000 000e0000
      I (85) boot:  4 ota_0            OTA app          00 10 00100000 00180000
      I (92) boot:  5 ota_1            OTA app          00 11 00280000 00180000
      I (100) boot: End of partition table
      I (104) esp_image: segment 0: paddr=00100020 vaddr=3f000020 size=28958h (166232) map
      I (146) esp_image: segment 1: paddr=00128980 vaddr=3ff9e02c size=00004h (     4) load
      I (146) esp_image: segment 2: paddr=0012898c vaddr=3ffc2f70 size=036f4h ( 14068) load
      I (155) esp_image: segment 3: paddr=0012c088 vaddr=40022000 size=03f90h ( 16272) load
      I (164) esp_image: segment 4: paddr=00130020 vaddr=40080020 size=d2214h (860692) map
      I (340) esp_image: segment 5: paddr=0020223c vaddr=40025f90 size=0cfdch ( 53212) load
      I (354) esp_image: segment 6: paddr=0020f220 vaddr=40070000 size=0002ch (    44) load
      I (363) boot: Loaded app from partition at offset 0x100000
      I (363) boot: Disabling RNG early entropy source...
      at param mode: 1
      AT cmd port:uart1 tx:17 rx:21 cts:20 rts:19 baudrate:115200
      module_name: MINI
      max tx power=78, ret=0
      v3.4.0.0-dev
