NEOgHacking/DMXion_4Port_Node/Firmware/esp-at-5.0.0.0/docs/_static/get_started/download_guide/download_multi_bin_esp32s2.png

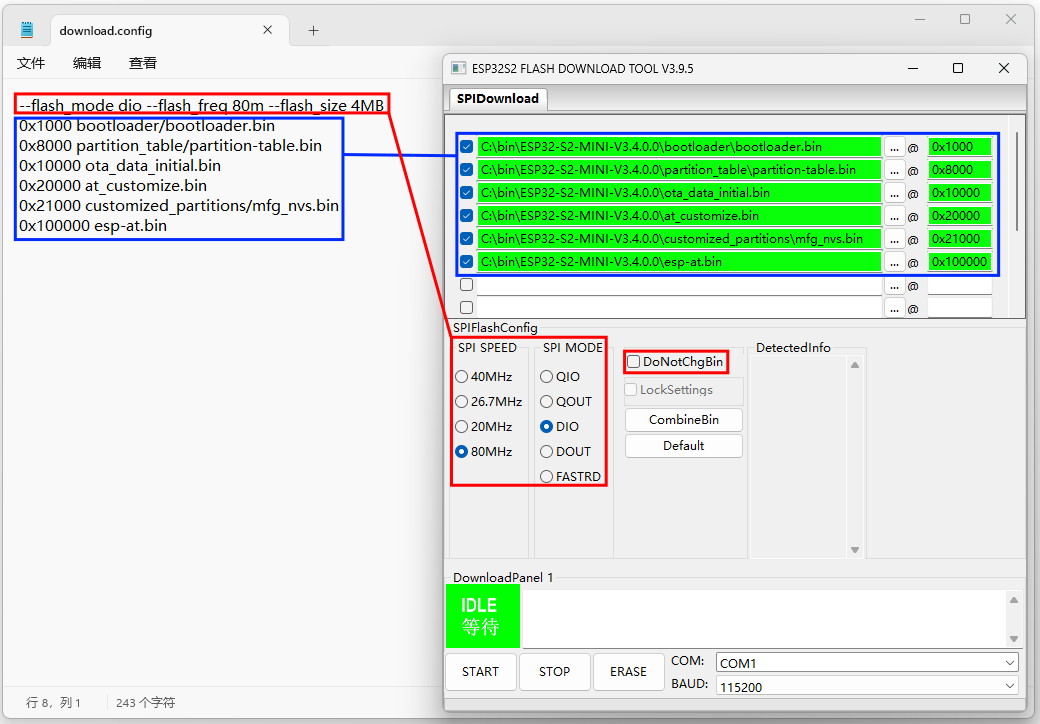
Firmware/esp-at-5.0.0.0/docs/_static/get_started/download_guide/download_multi_bin_esp32s2.png
