NEOgHacking/DMXion_4Port_Node/Firmware/esp-at-5.0.0.0/docs/_static/get_started/download_guide/download_one_bin_esp32c5.png

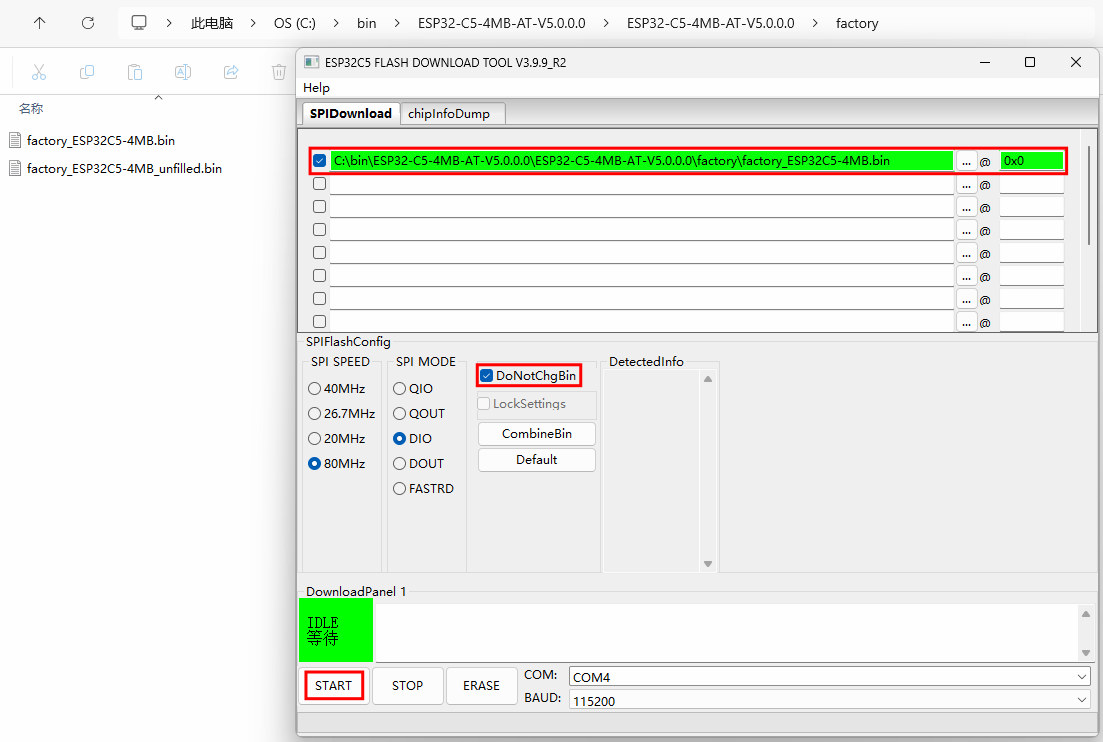
Firmware/esp-at-5.0.0.0/docs/_static/get_started/download_guide/download_one_bin_esp32c5.png
