NEOgHacking/DMXion_4Port_Node/Firmware/esp-at-5.0.0.0/docs/_static/RainMaker/nova_provisioning_starts.png

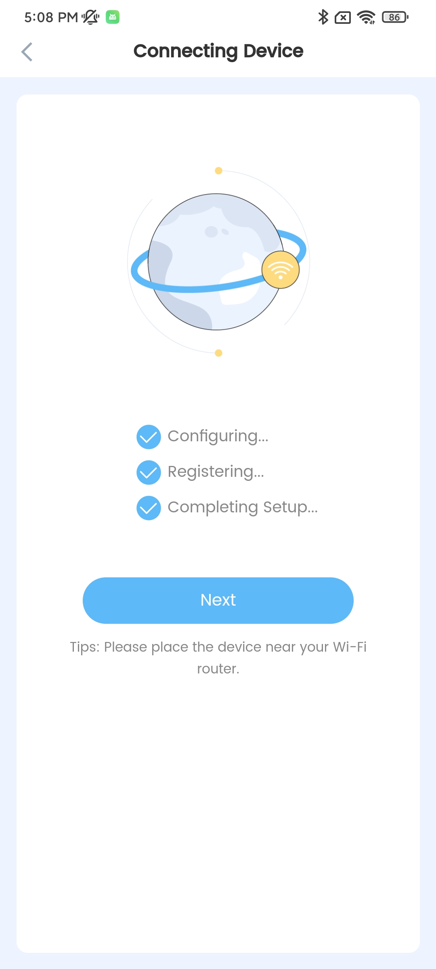
Firmware/esp-at-5.0.0.0/docs/_static/RainMaker/nova_provisioning_starts.png
