NEOgHacking/DMXion_4Port_Node/Firmware/esp-at-5.0.0.0/docs/_static/RainMaker/rest_api_get_request_id.png

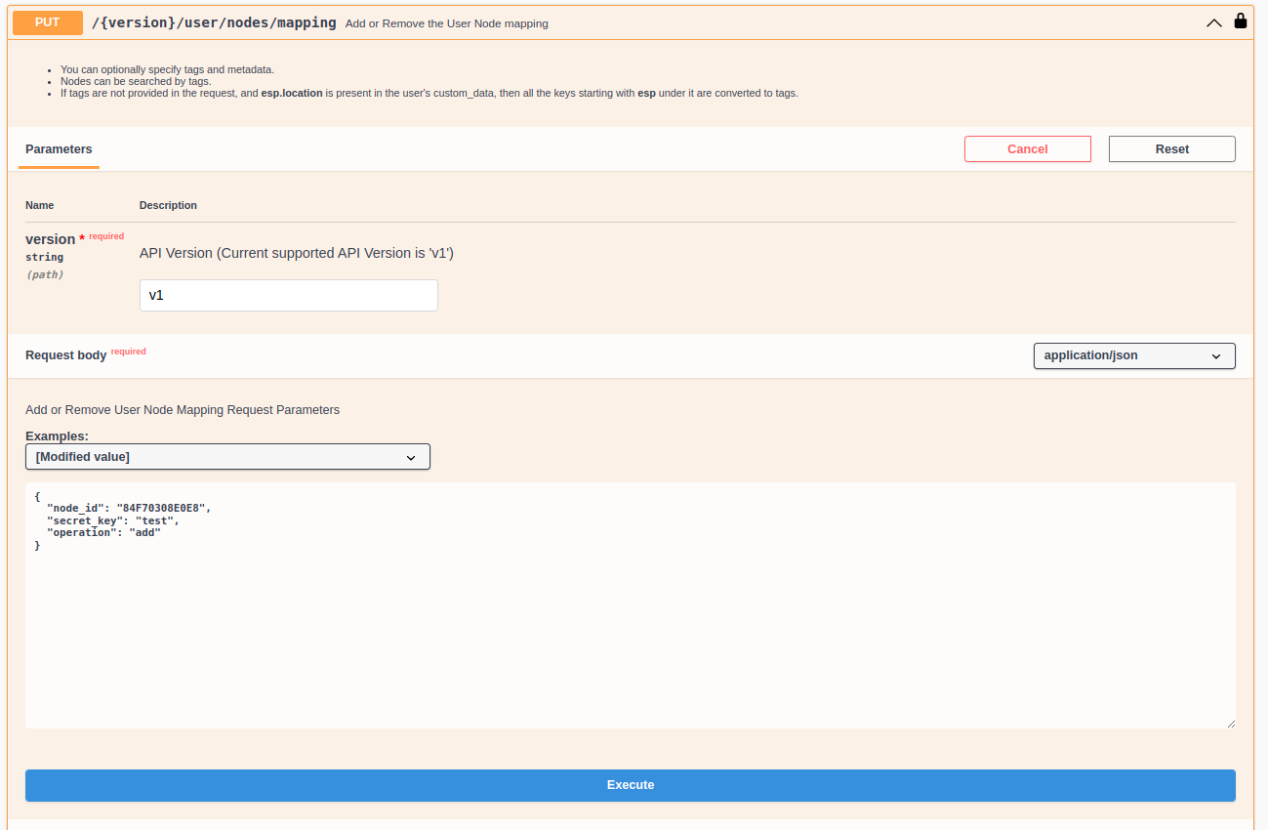
Firmware/esp-at-5.0.0.0/docs/_static/RainMaker/rest_api_get_request_id.png
