NEOgHacking/DMXion_4Port_Node/Firmware/esp-at-5.0.0.0/docs/_static/RainMaker/rest_api_get_user_details.png

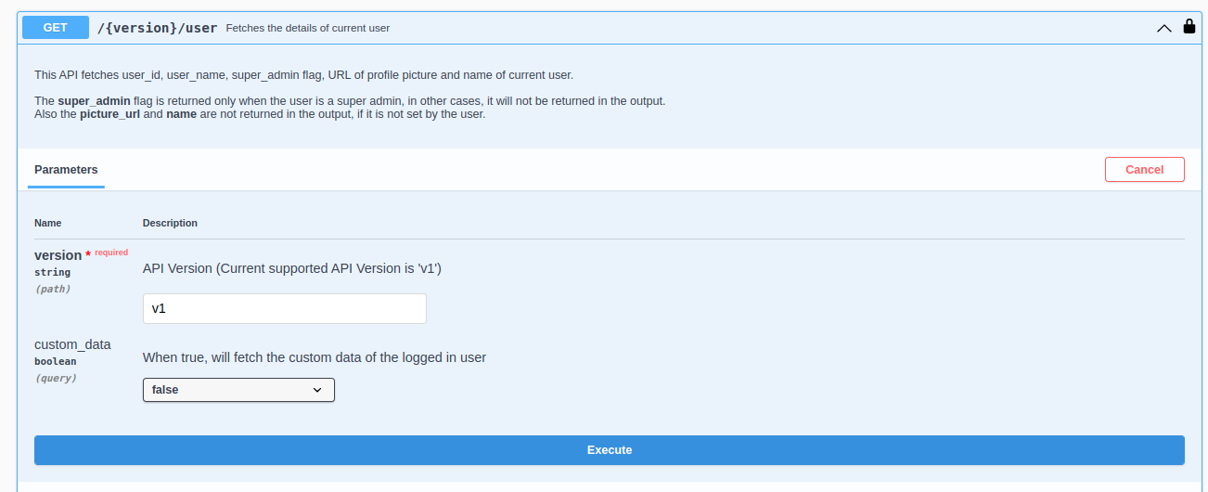
Firmware/esp-at-5.0.0.0/docs/_static/RainMaker/rest_api_get_user_details.png
